thebenheckshow/210-tbhs-raspberry-s-pi-cam/Pictures/IMG_20151013_194701968.jpg

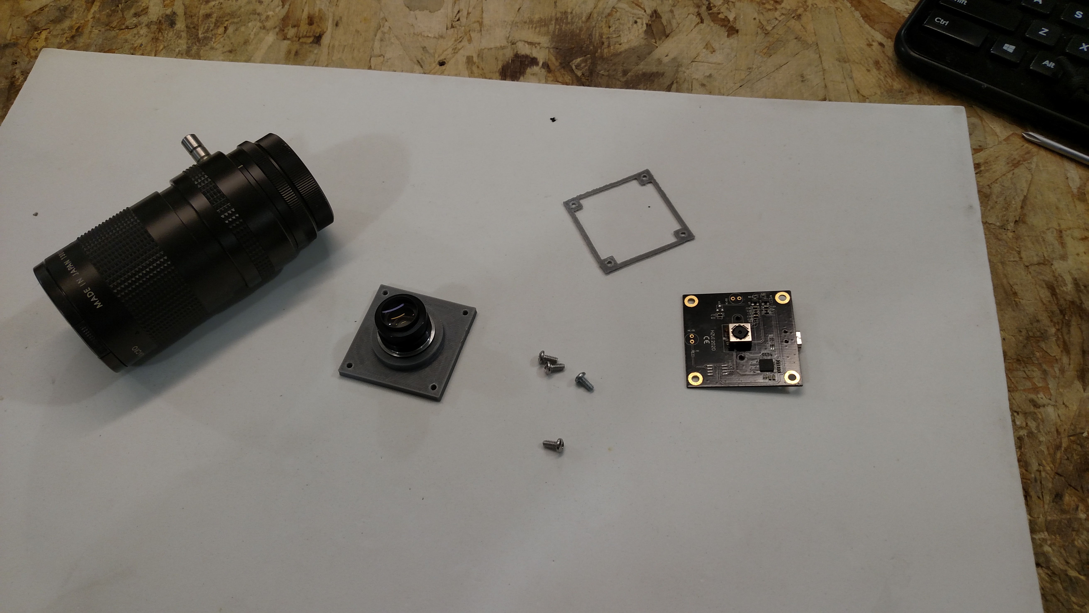
Pictures/IMG_20151013_194701968.jpg
