thebenheckshow/210-tbhs-raspberry-s-pi-cam/Pictures/IMG_20151013_195835702.jpg

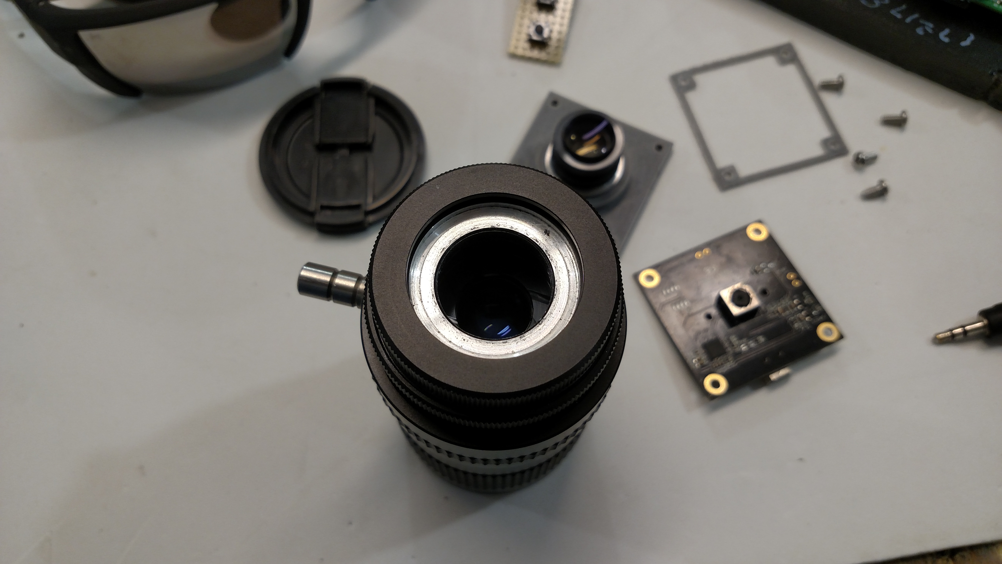
Pictures/IMG_20151013_195835702.jpg
