thebenheckshow/210-tbhs-raspberry-s-pi-cam/Pictures/IMG_20151013_200347834_HDR.jpg

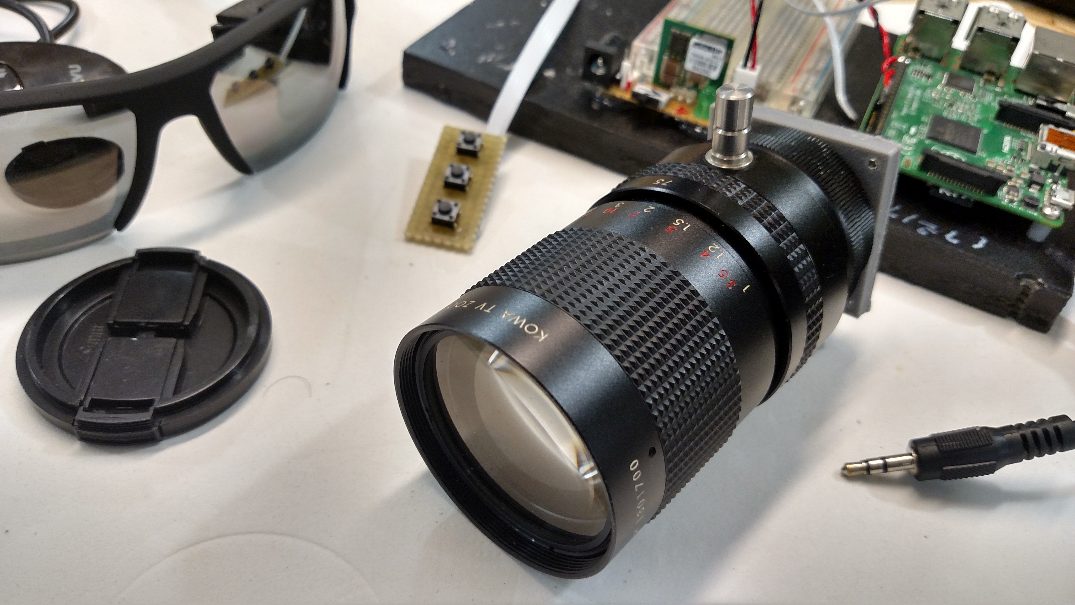
Pictures/IMG_20151013_200347834_HDR.jpg
