thebenheckshow/210-tbhs-raspberry-s-pi-cam/Pictures/IMG_20151013_200801730.jpg

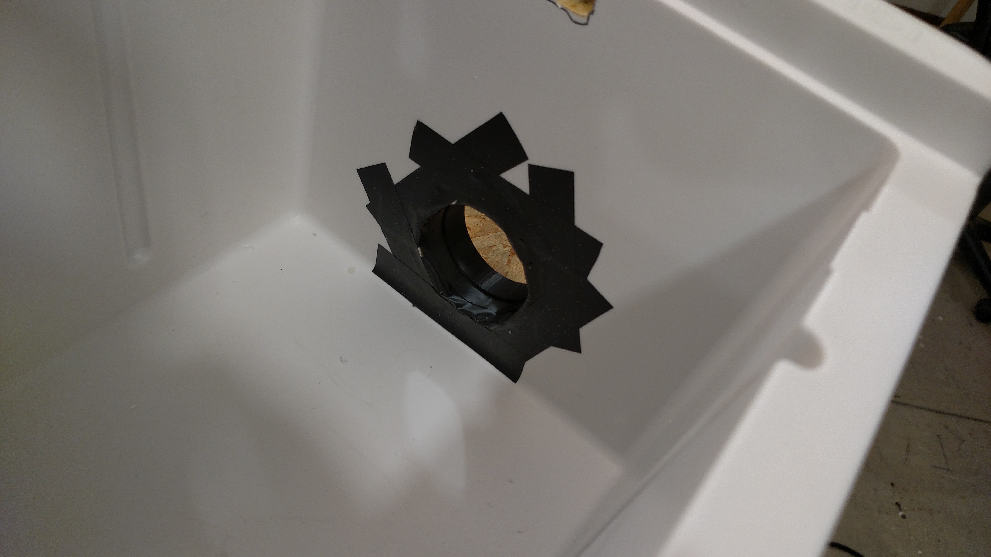
Pictures/IMG_20151013_200801730.jpg
