thebenheckshow/210-tbhs-raspberry-s-pi-cam/Pictures/IMG_20151013_200846267.jpg

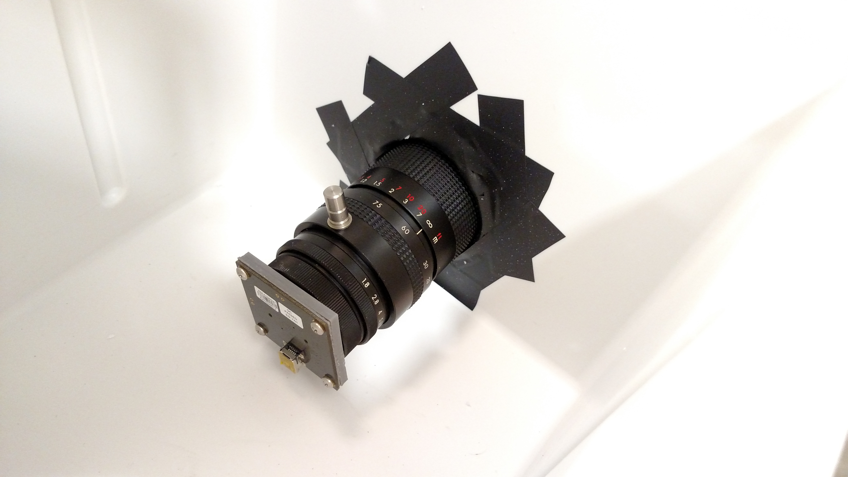
Pictures/IMG_20151013_200846267.jpg
