thebenheckshow/210-tbhs-raspberry-s-pi-cam/Pictures/IMG_20151013_201024064.jpg

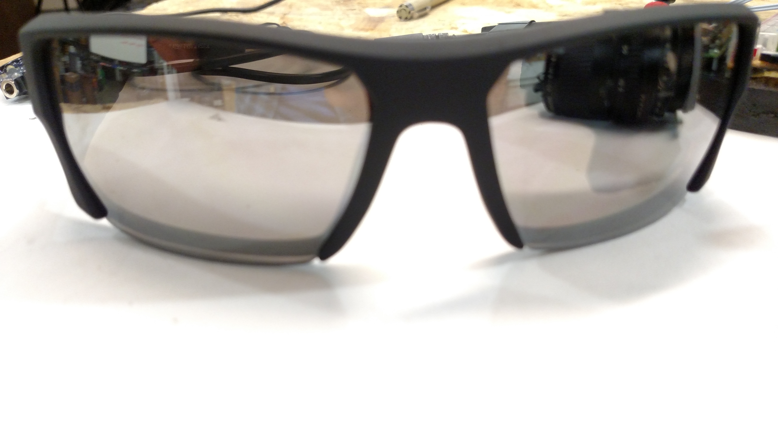
Pictures/IMG_20151013_201024064.jpg
