thebenheckshow/210-tbhs-raspberry-s-pi-cam/Design/STL/servo pulley.stl

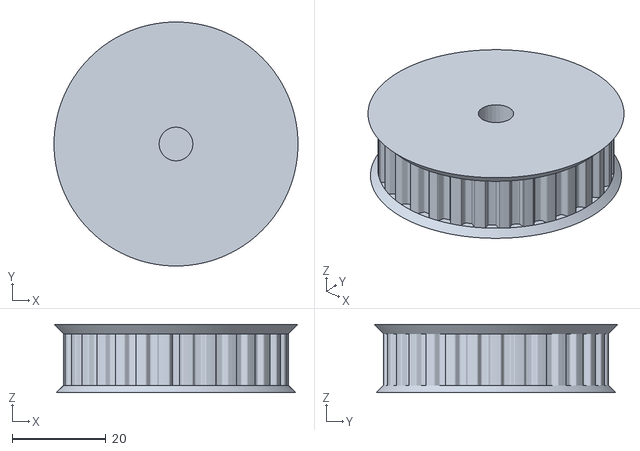
[picture p41: CAD file, 2015-11-20]
Design/STL/servo pulley.stl
52.0 x 52.0 x 14.5
